GunnAeronautics/mower6.0/Flight Data Shenanigans/Python Testing/datalog2.csv

time | x accl | y accl | z accl | gyro x | gyro y | gyro z | pressure
7323 | -0.18 | 0.11 | 9.90 | -0.01 | -0.08 | 0.02 | 1019.73
7345 | -0.09 | 0.07 | 9.79 | -0.01 | 0.01 | 0.01 | 1019.73
7366 | -0.15 | 0.08 | 9.88 | -0.02 | 0.05 | 0.01 | 1019.71
7388 | -0.17 | 0.07 | 9.94 | -0.02 | 0.08 | 0.00 | 1019.71
7410 | -0.16 | 0.05 | 10.09 | -0.01 | 0.09 | 0.00 | 1019.73
7431 | -0.11 | 0.20 | 10.15 | 0.02 | 0.10 | -0.00 | 1019.73
7453 | -0.09 | 0.24 | 10.16 | 0.02 | 0.10 | -0.01 | 1019.71
7475 | -0.11 | 0.23 | 10.13 | 0.02 | 0.08 | -0.02 | 1019.71
7496 | -0.05 | 0.29 | 10.10 | 0.01 | 0.05 | -0.02 | 1019.71
7518 | -0.07 | 0.20 | 10.13 | -0.00 | 0.01 | -0.03 | 1019.71
7545 | 0.08 | 0.30 | 10.05 | -0.00 | -0.03 | -0.04 | 1019.70
7566 | -0.00 | 0.20 | 10.03 | -0.01 | -0.05 | -0.05 | 1019.71
7588 | 0.09 | 0.25 | 10.11 | -0.01 | -0.05 | -0.05 | 1019.71
7610 | 0.11 | 0.33 | 10.05 | -0.02 | -0.01 | -0.05 | 1019.71
7632 | -0.10 | 0.23 | 10.28 | -0.04 | 0.04 | -0.06 | 1019.71
7653 | -0.09 | 0.27 | 10.33 | -0.04 | 0.07 | -0.07 | 1019.75
7675 | -0.14 | 0.23 | 10.16 | -0.02 | 0.05 | -0.07 | 1019.75
7697 | -0.01 | 0.19 | 10.04 | 0.01 | 0.00 | -0.07 | 1019.76
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
